Community-Sensor-Lab/Air-Quality-Sensor-ESP32/Contents/air_mon_system1.png

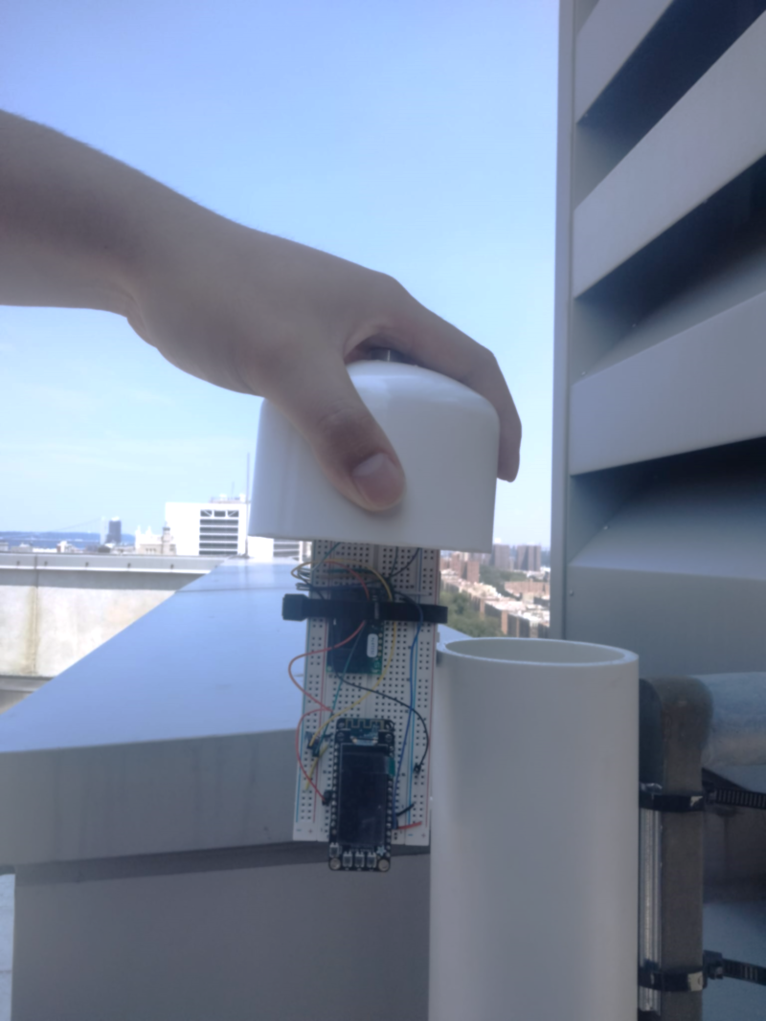
Contents/air_mon_system1.png
