Community-Sensor-Lab/Air-Quality-Sensor-ESP32/Contents/air_mon_system_sqr1.jpg

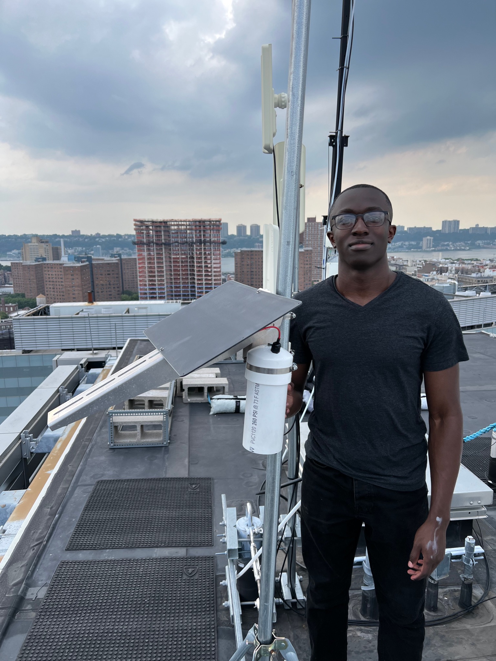
Contents/air_mon_system_sqr1.jpg
