Community-Sensor-Lab/Air-Quality-Sensor-ESP32/Contents/CSL_AQS_solar_sqr.png

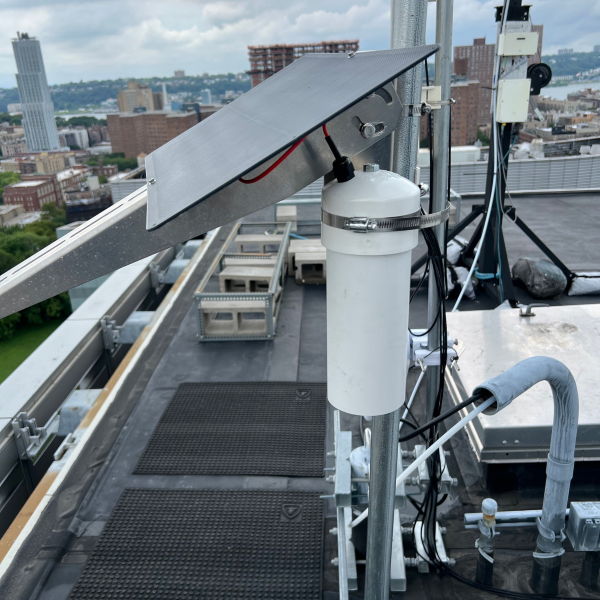
Contents/CSL_AQS_solar_sqr.png
