Community-Sensor-Lab/Air-Quality-Sensor-ESP32/Contents/image-52.png

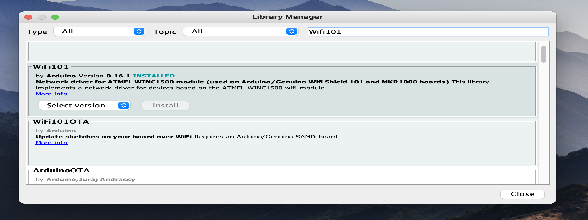
Contents/image-52.png
