Community-Sensor-Lab/Air-Quality-Sensor-ESP32/Contents/image-53.png

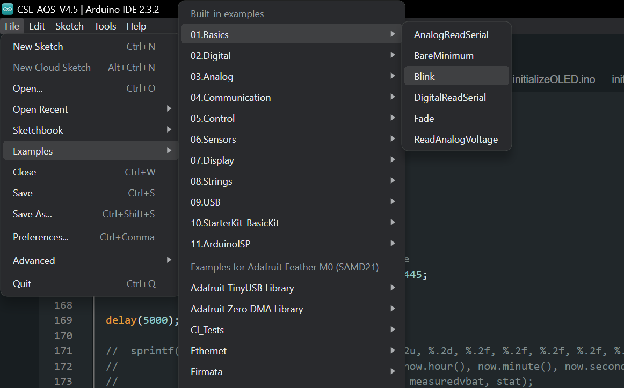
Contents/image-53.png
