Community-Sensor-Lab/Air-Quality-Sensor-ESP32/Contents/image-54.png

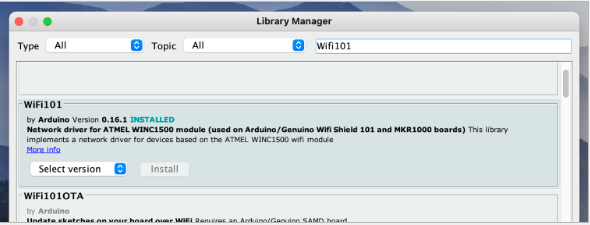
Contents/image-54.png
