Community-Sensor-Lab/Air-Quality-Sensor-ESP32/Contents/image.png

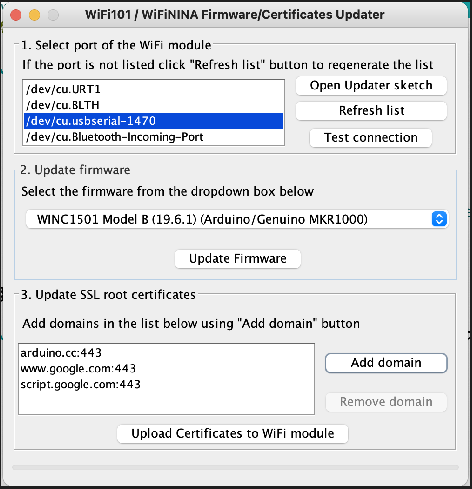
Contents/image.png
