Community-Sensor-Lab/Air-Quality-Sensor-ESP32/images/Adafruit BME280.png

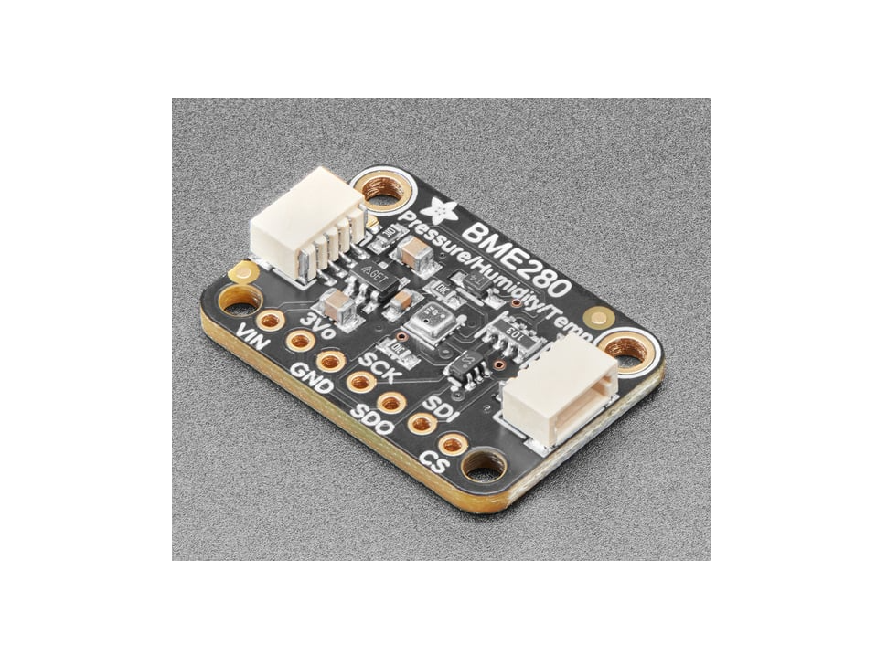
images/Adafruit BME280.png
