Community-Sensor-Lab/Air-Quality-Sensor-ESP32/images/Adafruit_SCD-41.png

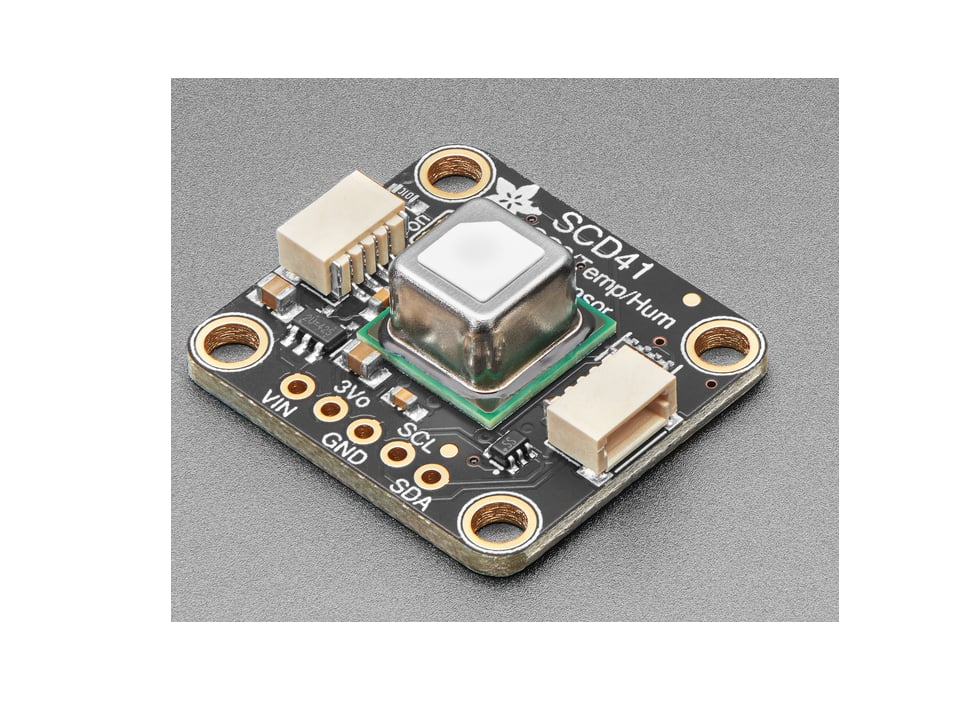
images/Adafruit_SCD-41.png
