Community-Sensor-Lab/Air-Quality-Sensor-ESP32/images/Addalogger_FeatherWing.png

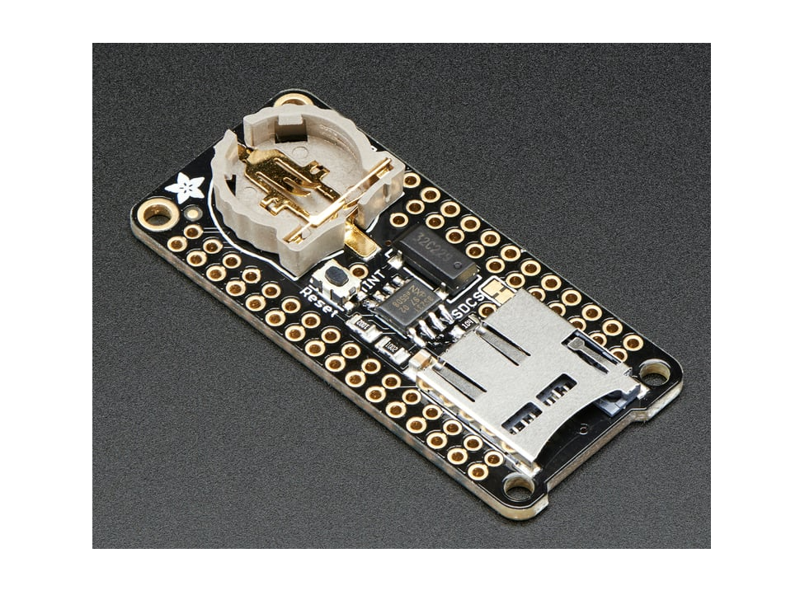
images/Addalogger_FeatherWing.png
