Community-Sensor-Lab/Air-Quality-Sensor-ESP32/images/air_mon_system_sqr.png

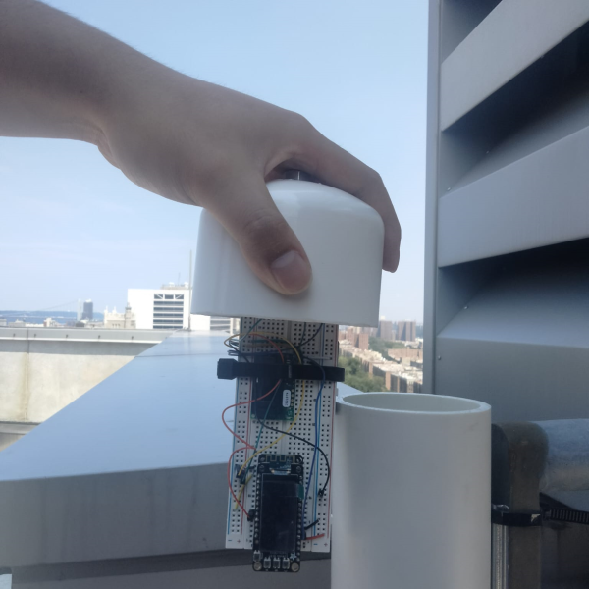
images/air_mon_system_sqr.png
