Community-Sensor-Lab/Air-Quality-Sensor-ESP32/images/Charts_Spreadsheets7.JPG

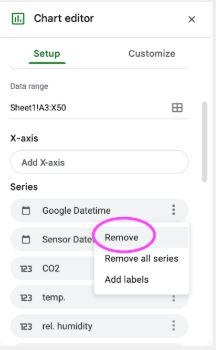
images/Charts_Spreadsheets7.JPG
