Community-Sensor-Lab/Air-Quality-Sensor-ESP32/images/CSL_AQS_solar2.jpg

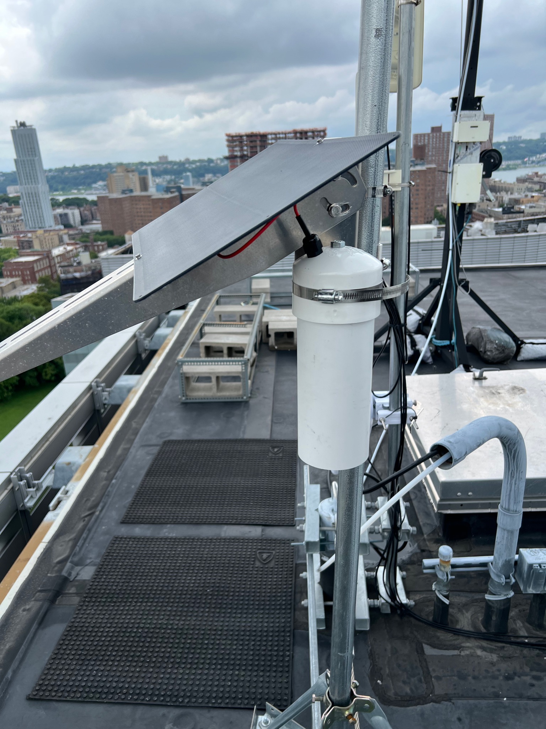
images/CSL_AQS_solar2.jpg
