Community-Sensor-Lab/Air-Quality-Sensor-ESP32/images/Feather_M0_Wifi.jpg

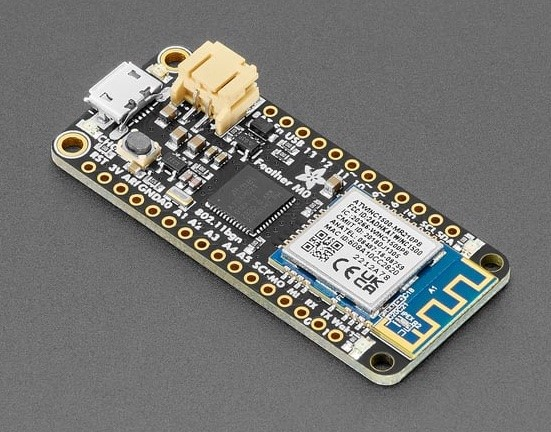
images/Feather_M0_Wifi.jpg
