Community-Sensor-Lab/Air-Quality-Sensor-ESP32/images/FeatherWing_OLED.png

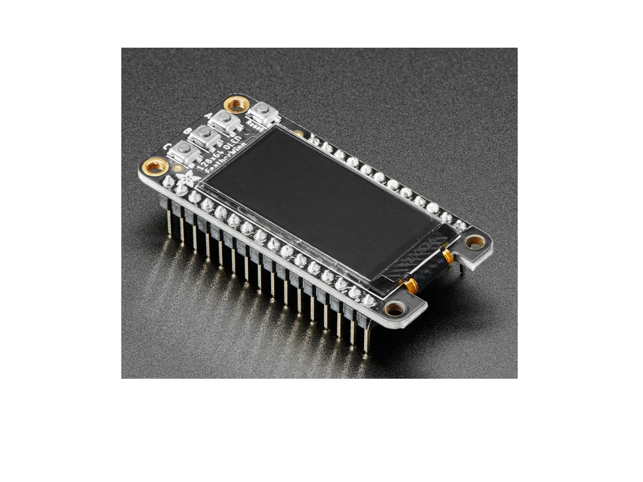
images/FeatherWing_OLED.png
