Community-Sensor-Lab/Air-Quality-Sensor-ESP32/images/Google-Logging-Spreadsheet.png

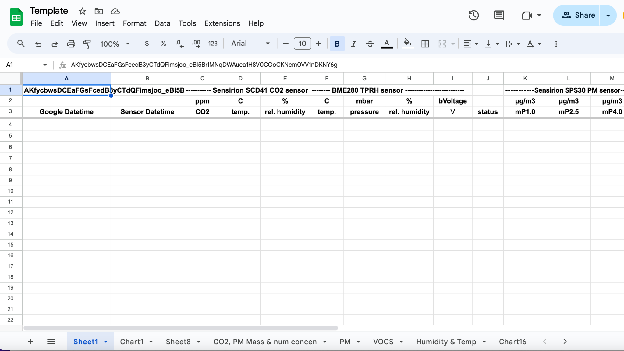
images/Google-Logging-Spreadsheet.png
