Community-Sensor-Lab/Air-Quality-Sensor-ESP32/images/hero_spr.png

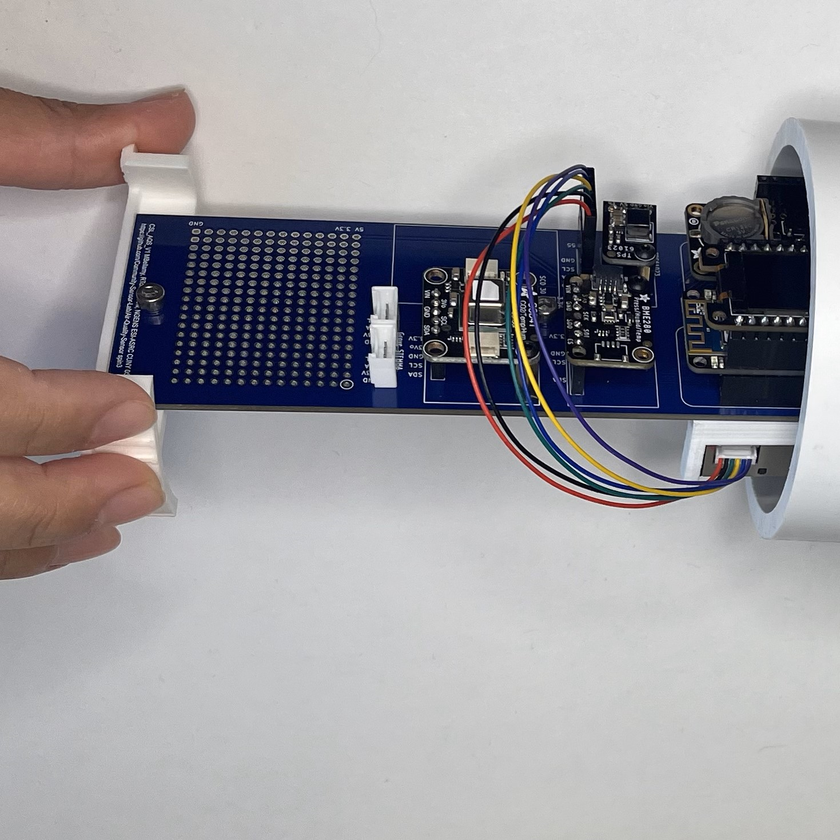
images/hero_spr.png
