Community-Sensor-Lab/Air-Quality-Sensor-ESP32/images/hero_sqr3.png

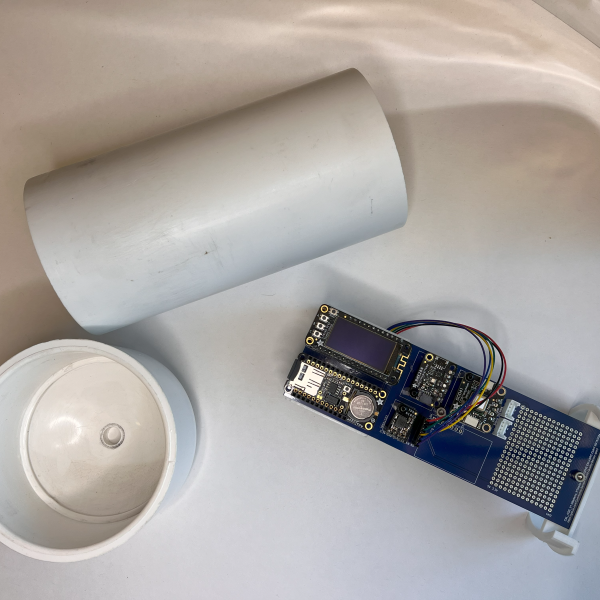
images/hero_sqr3.png
