Community-Sensor-Lab/Air-Quality-Sensor-ESP32/images/OLED.jpg

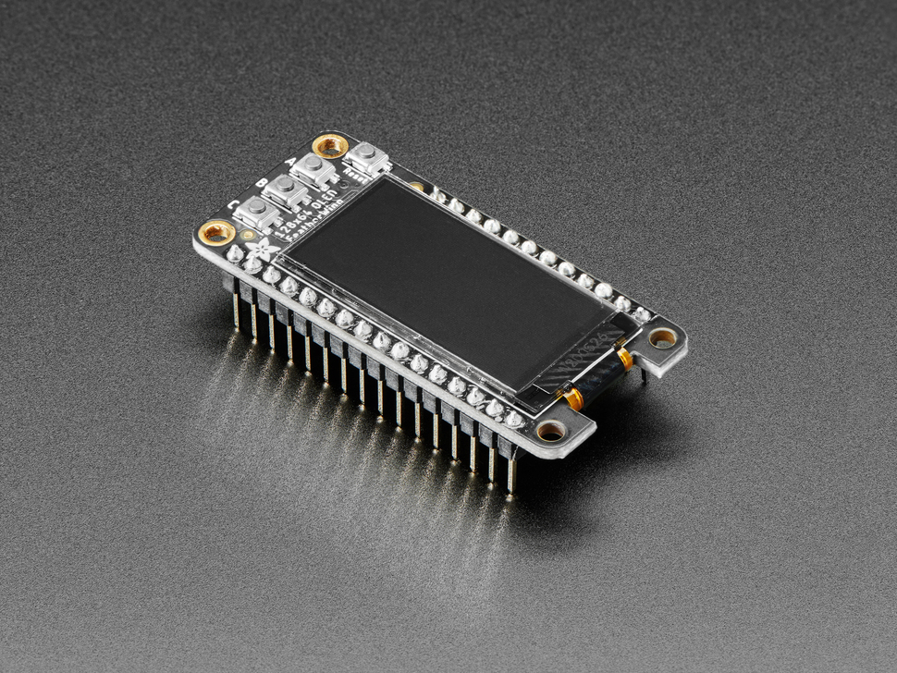
images/OLED.jpg
