Community-Sensor-Lab/Air-Quality-Sensor-ESP32/images/SEN55_PM-AQS.png

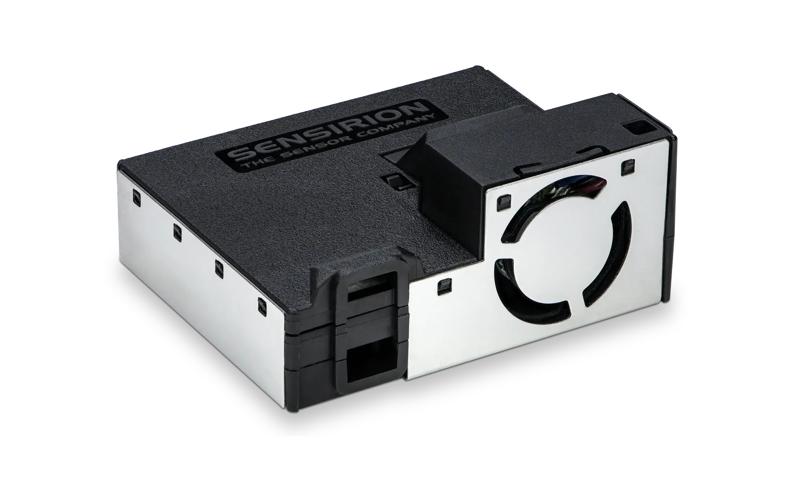
images/SEN55_PM-AQS.png
