Community-Sensor-Lab/Air-Quality-Sensor-ESP32/M_CAD/M_CAD-Inventor2025/STL Files/PCB Soldering Stand for Ultimaker 5.stl

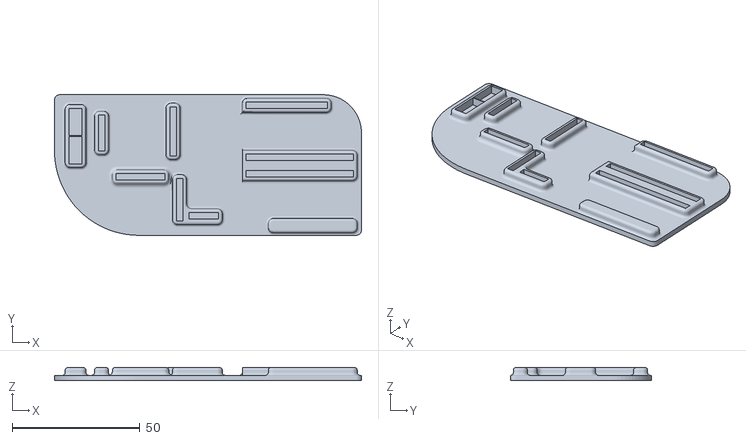
[picture p112: CAD file, 2026-02-05]
M_CAD/M_CAD-Inventor2025/STL Files/PCB Soldering Stand for Ultimaker 5.stl
120.0 x 55.0 x 5.00
