Community-Sensor-Lab/Air-Quality-Sensor-ESP32/M_CAD/M_CAD-Inventor2025/STP Files/Solar Board Mount V1.stp

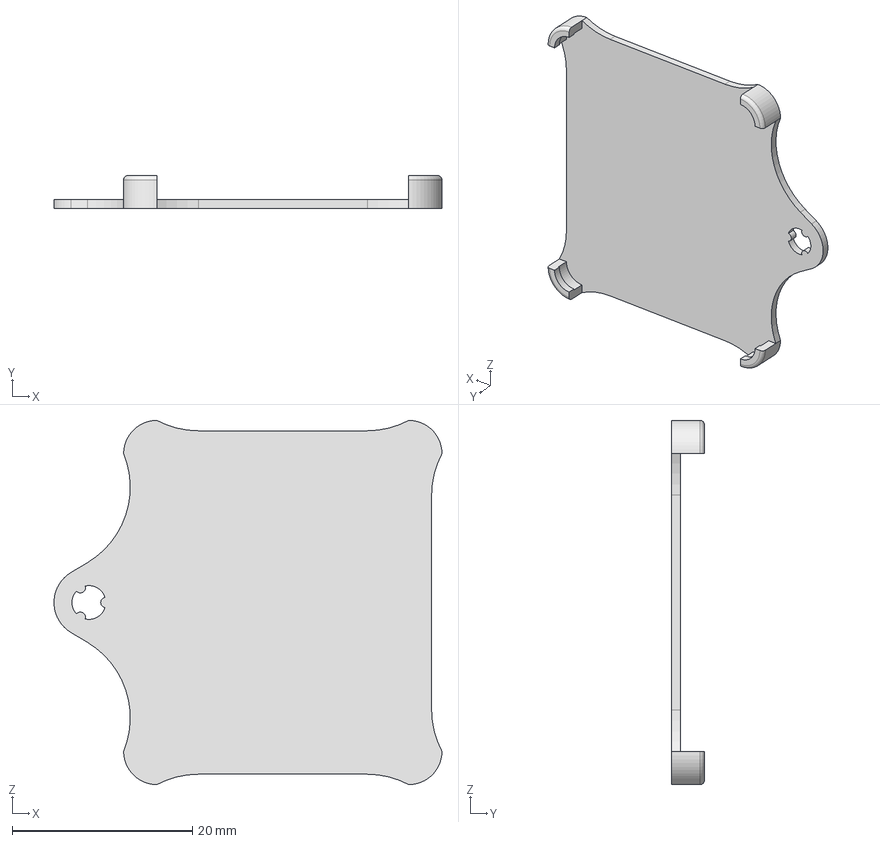
[picture p113: CAD file, 2026-02-05]
M_CAD/M_CAD-Inventor2025/STP Files/Solar Board Mount V1.stp
43.0 x 3.67 x 40.4 mm
