Community-Sensor-Lab/Air-Quality-Sensor-ESP32/M_CAD/M_CAD-Inventor2025/Air Quality Sensor/4654 MiniBoost 5V.step

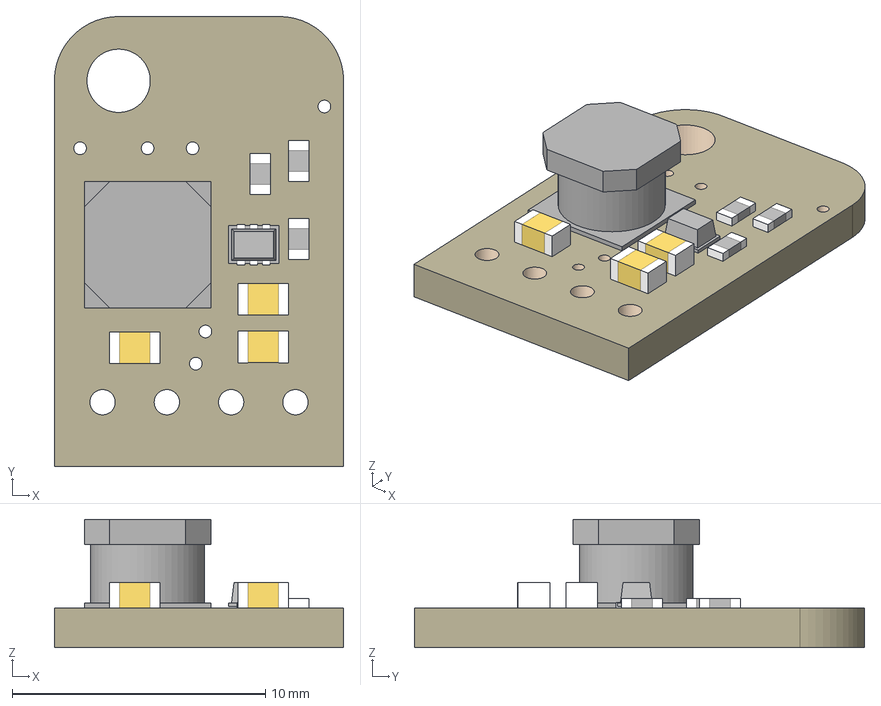
[picture p114: CAD file, 2026-02-05]
M_CAD/M_CAD-Inventor2025/Air Quality Sensor/4654 MiniBoost 5V.step
11.4 x 17.8 x 5.07 mm
Board
22uF x 3
100K x 3
TPS61023
1uH
