Community-Sensor-Lab/Air-Quality-Sensor-ESP32/M_CAD/M_CAD-Inventor2025/STL Files/Horizontal Base (Print 2).stl

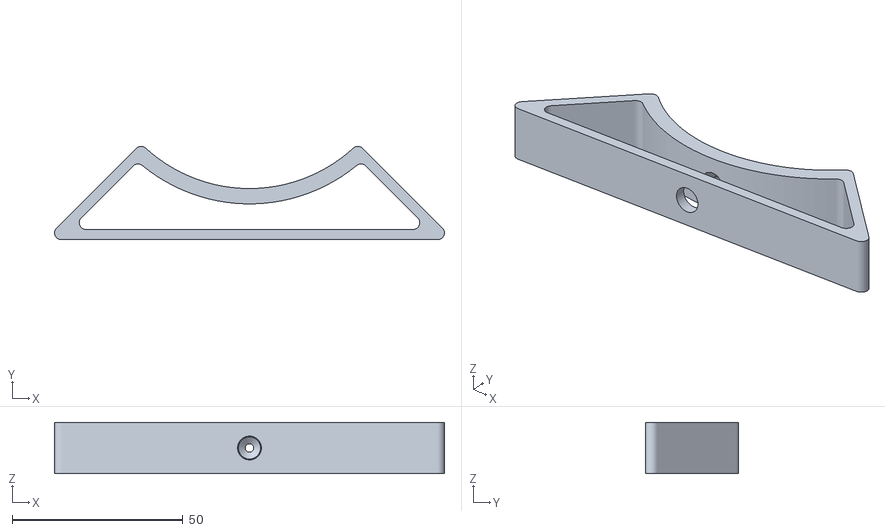
[picture p115: CAD file, 2026-02-05]
M_CAD/M_CAD-Inventor2025/STL Files/Horizontal Base (Print 2).stl
114.3 x 27.4 x 15.0
