Community-Sensor-Lab/Air-Quality-Sensor-ESP32/M_CAD/M_CAD-Inventor2025/STP Files/SEN5X Mount V4 Antena.stp

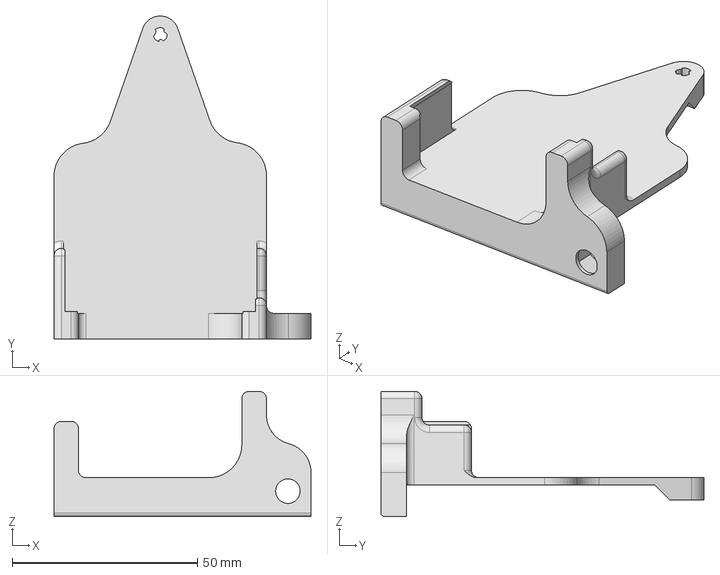
[picture p116: CAD file, 2026-02-05]
M_CAD/M_CAD-Inventor2025/STP Files/SEN5X Mount V4 Antena.stp
69.3 x 87.1 x 33.8 mm
