Community-Sensor-Lab/Air-Quality-Sensor-ESP32/M_CAD/M_CAD-Inventor2025/Air Quality Sensor/4755 USB Solar Charger.step

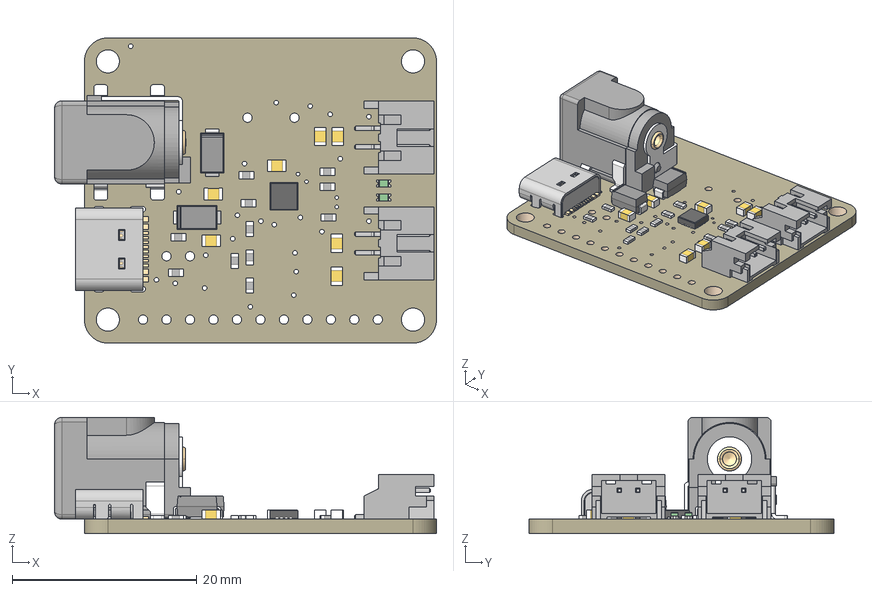
[picture p118: CAD file, 2026-02-05]
M_CAD/M_CAD-Inventor2025/Air Quality Sensor/4755 USB Solar Charger.step
41.3 x 33.0 x 12.6 mm
Board
JST 2PH x 2
10uF x 7
SK34A x 2
GREEN x 2
10K x 11
USB Type C
2.1mm DC
BQ24074
