Community-Sensor-Lab/Air-Quality-Sensor-ESP32/M_CAD/M_CAD-Inventor2025/Air Quality Sensor/4650 OLED FeatherWing.step

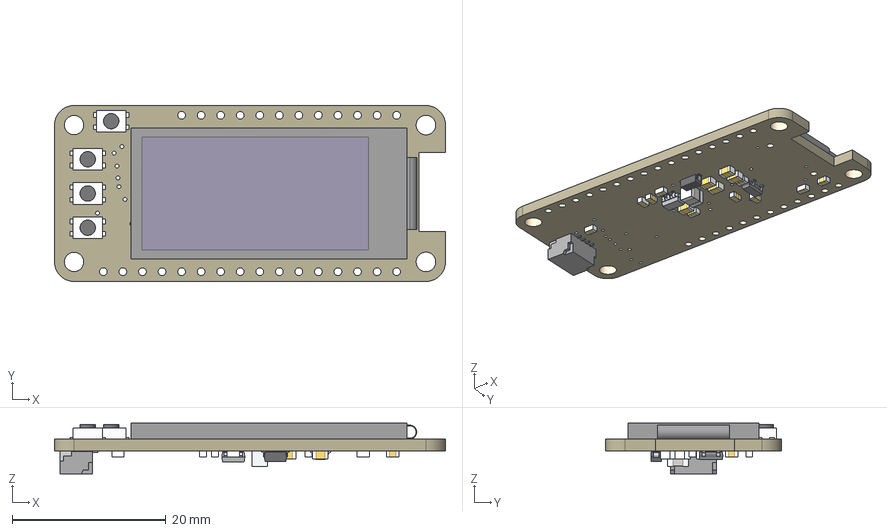
[picture p119: CAD file, 2026-02-05]
M_CAD/M_CAD-Inventor2025/Air Quality Sensor/4650 OLED FeatherWing.step
50.8 x 22.9 x 6.59 mm
Board
10uF/16V x 5
0.1uF x 10
KMR2 x 4
APX803
OLED_128X64_SH1107
FAN5331SX
10uH
MBR120
STEMMA_I2C_QT
