Community-Sensor-Lab/Air-Quality-Sensor-ESP32/M_CAD/M_CAD-Inventor2025/Air Quality Sensor/Grove socket.SLDPRT

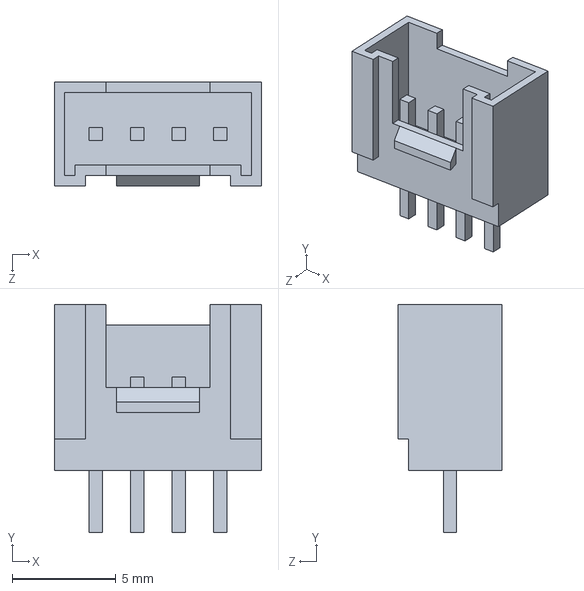
[picture p120: CAD file, 2026-02-05]
M_CAD/M_CAD-Inventor2025/Air Quality Sensor/Grove socket.SLDPRT
10.0 x 11.0 x 5.00 mm
