Community-Sensor-Lab/Air-Quality-Sensor-ESP32/M_CAD/M_CAD-Inventor2025/Air Quality Sensor/3010 Adafruit Feather M0 WiFi.step

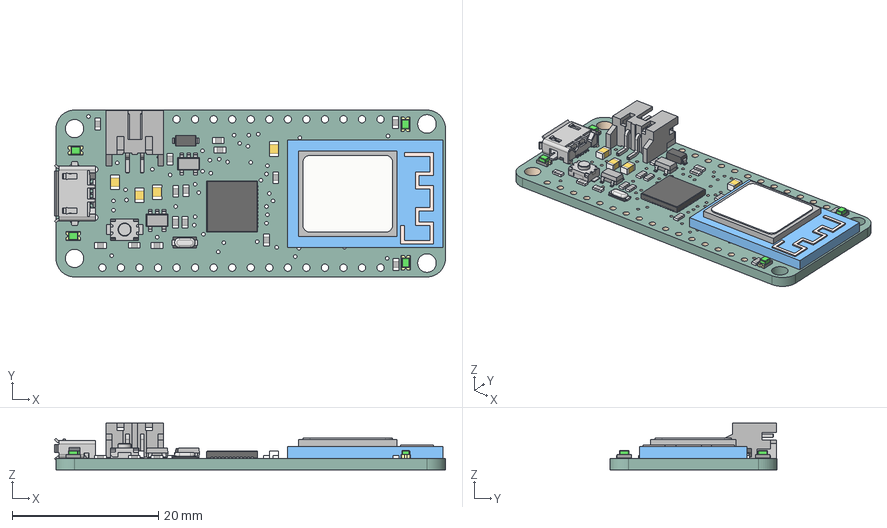
[picture p121: CAD file, 2026-02-05]
M_CAD/M_CAD-Inventor2025/Air Quality Sensor/3010 Adafruit Feather M0 WiFi.step
53.5 x 22.9 x 6.37 mm
Board
10uF x 4
1k x 15
GREEN x 4
SPST_TACT-KMR2
microUSB
MCP73831T-2ACI/OT x 2
MBR120
1X16_ROUND
JSTPH
ATSAMD21G18_QFN
ATWINC1500_MR210PA
FEATHERLOGO
