Community-Sensor-Lab/Air-Quality-Sensor-ESP32/M_CAD/M_CAD-Inventor2025/Air Quality Sensor/5187 SCD-40 C02 Sensor.step

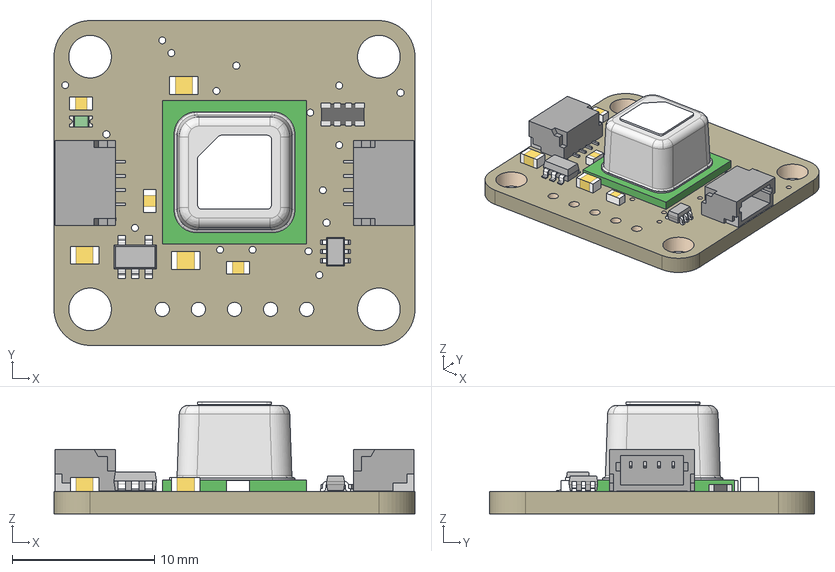
[picture p122: CAD file, 2026-02-05]
M_CAD/M_CAD-Inventor2025/Air Quality Sensor/5187 SCD-40 C02 Sensor.step
25.4 x 22.9 x 7.88 mm
Board
10uF x 3
AP2112K-3.3
0.1uF x 3
10K
BSS138
STEMMA_I2C_QT x 2
GREEN
SCD-41
