Community-Sensor-Lab/Air-Quality-Sensor-ESP32/M_CAD/M_CAD-Inventor2025/Air Quality Sensor/2652 BMP280 STEMMA QT.step

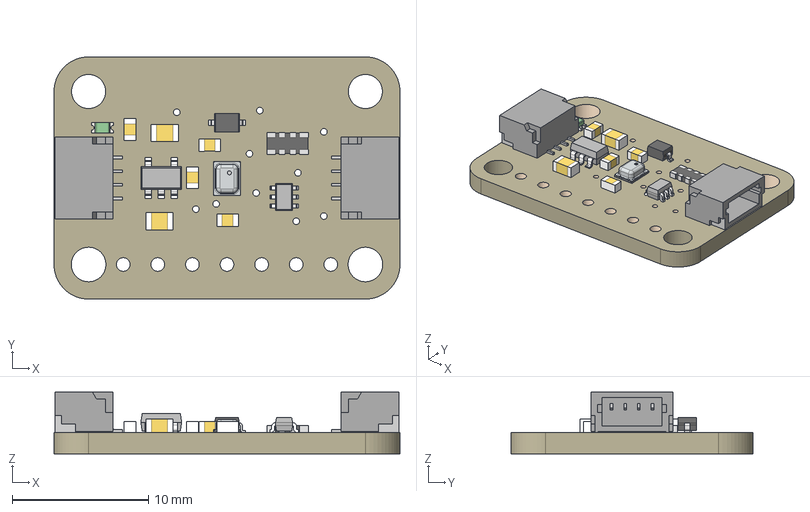
[picture p123: CAD file, 2026-02-05]
M_CAD/M_CAD-Inventor2025/Air Quality Sensor/2652 BMP280 STEMMA QT.step
25.4 x 17.8 x 4.53 mm
Board
10uF x 2
AP2112K-3.3
10K x 4
10K_1
BSS138
STEMMA_I2C_QT x 2
GREEN
1N4148
BMX280_COMBO
