Community-Sensor-Lab/Air-Quality-Sensor-ESP32/M_CAD/M_CAD-Inventor2025/Air Quality Sensor/head_f_3p.step

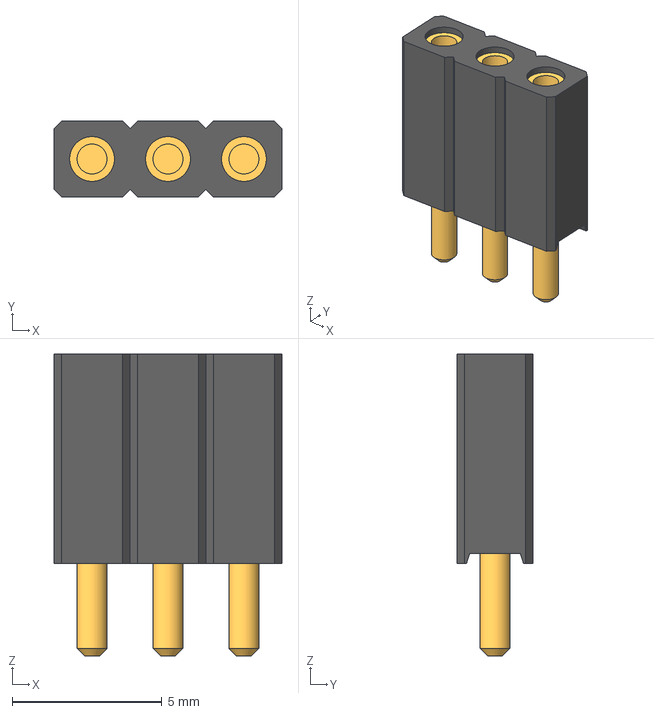
[picture p124: CAD file, 2026-02-05]
M_CAD/M_CAD-Inventor2025/Air Quality Sensor/head_f_3p.step
7.62 x 2.54 x 10.1 mm
