Community-Sensor-Lab/Air-Quality-Sensor-ESP32/images/Design-and-Assembly-of-PCB2.png

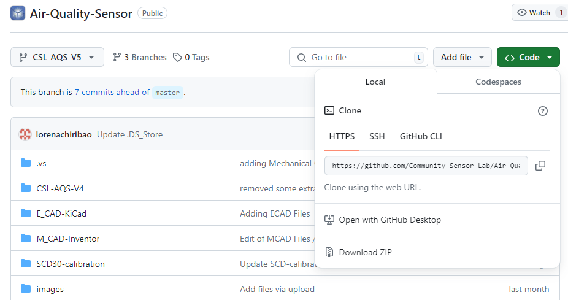
images/Design-and-Assembly-of-PCB2.png
