Community-Sensor-Lab/Air-Quality-Sensor-ESP32/images/Design-and-Assembly-of-PCB6.png

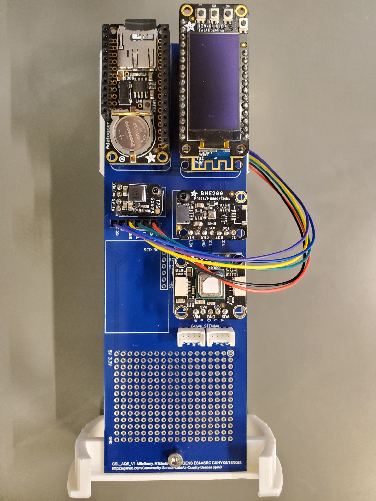
images/Design-and-Assembly-of-PCB6.png
