Community-Sensor-Lab/Air-Quality-Sensor-ESP32/images/installing_arduino1.JPG

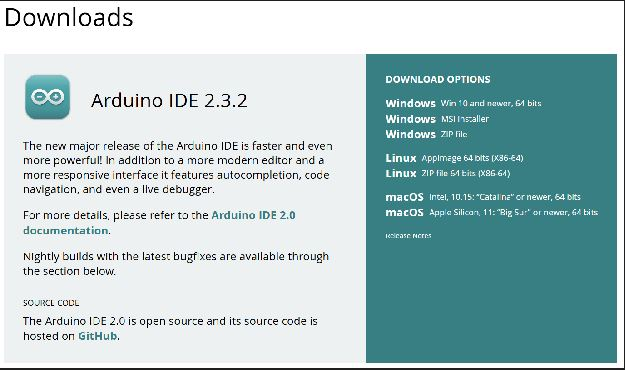
images/installing_arduino1.JPG
