Community-Sensor-Lab/Air-Quality-Sensor-ESP32/images/installing_arduino2.JPG

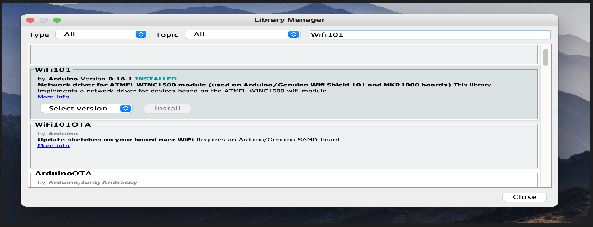
images/installing_arduino2.JPG
