Community-Sensor-Lab/Air-Quality-Sensor-ESP32/images/Make-Data-Graphs-Lines-and-Time-Series1.png

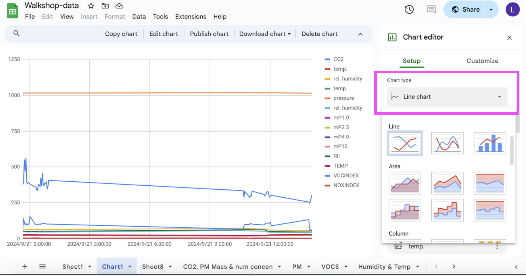
images/Make-Data-Graphs-Lines-and-Time-Series1.png
