Community-Sensor-Lab/Air-Quality-Sensor-ESP32/images/Make-Data-Graphs-Lines-and-Time-Series4.png

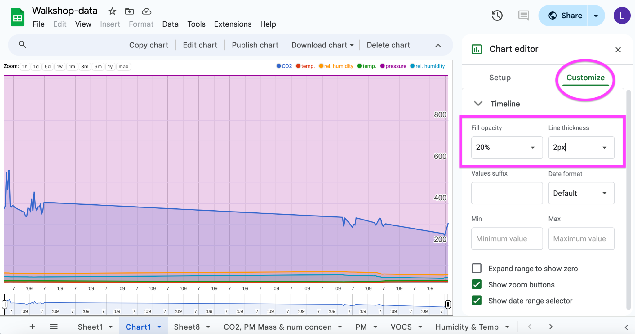
images/Make-Data-Graphs-Lines-and-Time-Series4.png
